tor1kk/TS_Tracker/software/Core/Inc/application_tasks.h

/*
 * tasks.h
 *
 *  Created on: May 8, 2024
 *      Author: Viktor
 */

#ifndef INC_APPLICARTION_TASKS_H_
#define INC_APPLICARTION_TASKS_H_

#include "main.h"


void reset_sim800(void);
void create_tasks(void);
void send_sms(SMS_t *sms);


#endif /* INC_APPLICARTION_TASKS_H_ */
